cfinke/Construction-grade-Backhoe-Loader/assets/Chassis Back.stl

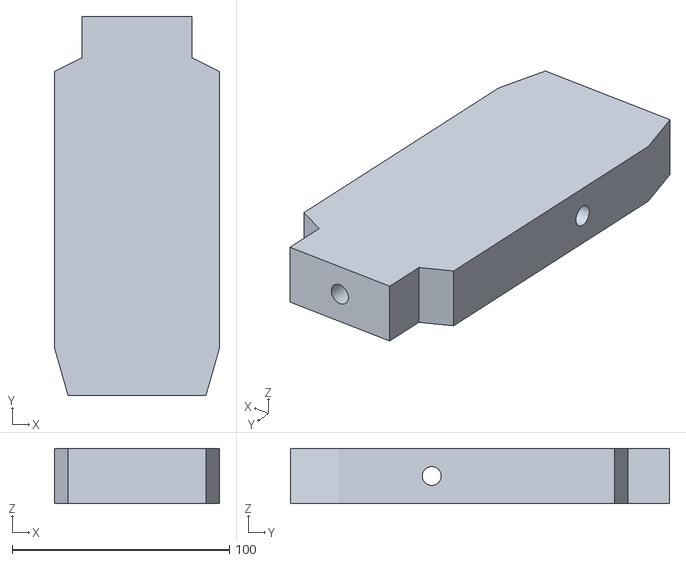
[picture p16: CAD file, 2014-10-20]
assets/Chassis Back.stl
76.2 x 174.6 x 25.4
