cfinke/Construction-grade-Backhoe-Loader/assets/Bucket.stl

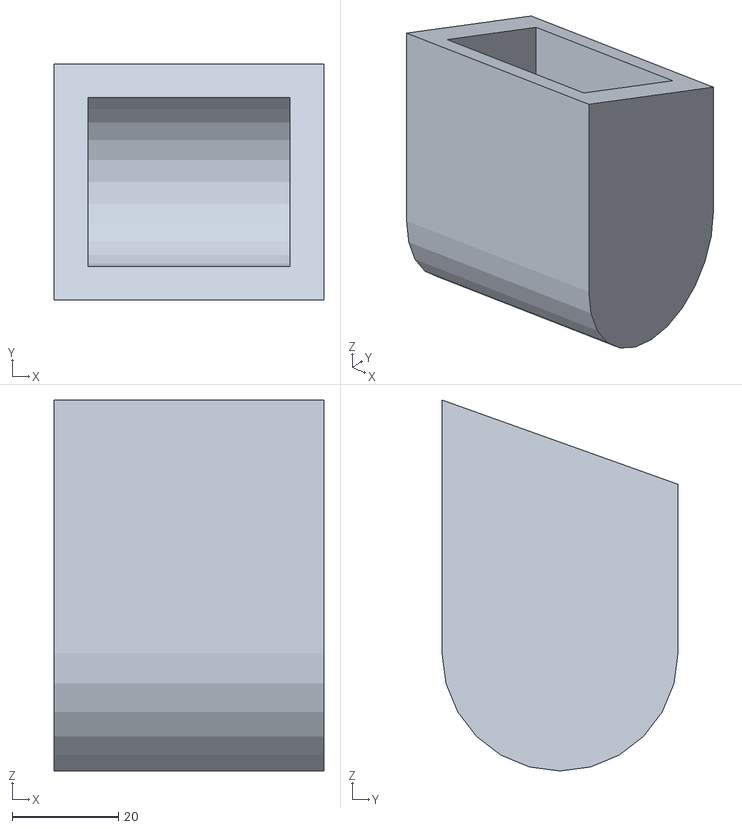
[picture p17: CAD file, 2014-10-20]
assets/Bucket.stl
50.8 x 44.4 x 69.9
