cfinke/Construction-grade-Backhoe-Loader/assets/Loader.stl

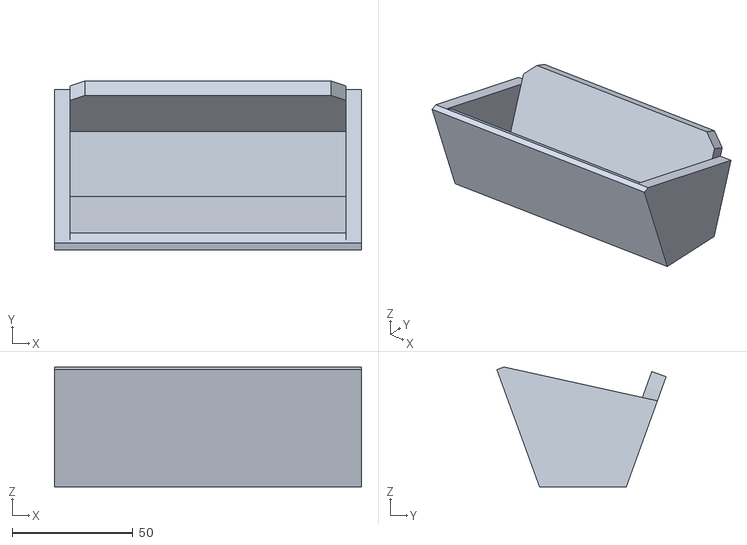
[picture p18: CAD file, 2014-10-20]
assets/Loader.stl
127.0 x 70.1 x 49.6
