cfinke/Construction-grade-Backhoe-Loader/assets/Loader Arm.stl

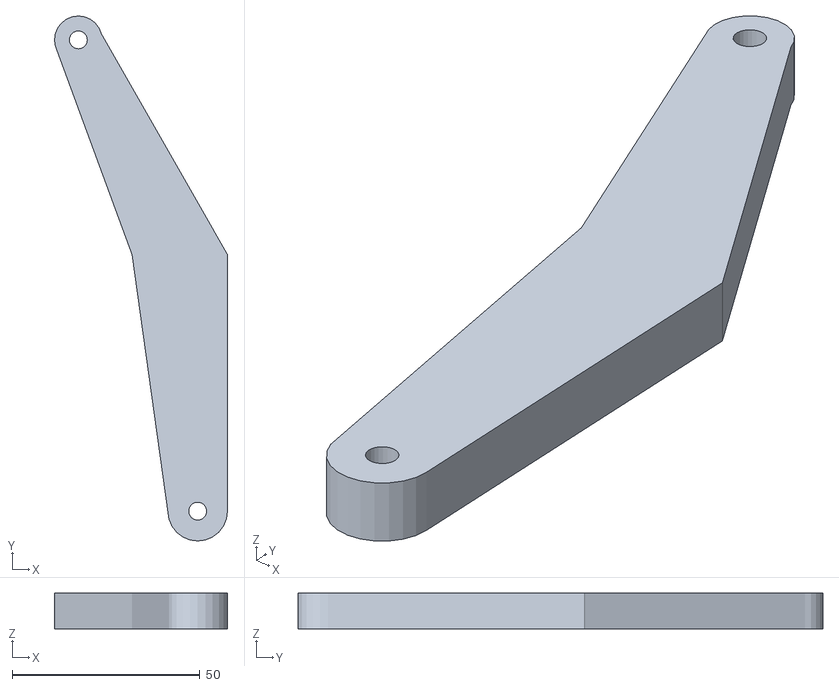
[picture p19: CAD file, 2014-10-20]
assets/Loader Arm.stl
46.0 x 139.7 x 9.52
