cfinke/Construction-grade-Backhoe-Loader/assets/Stick.stl

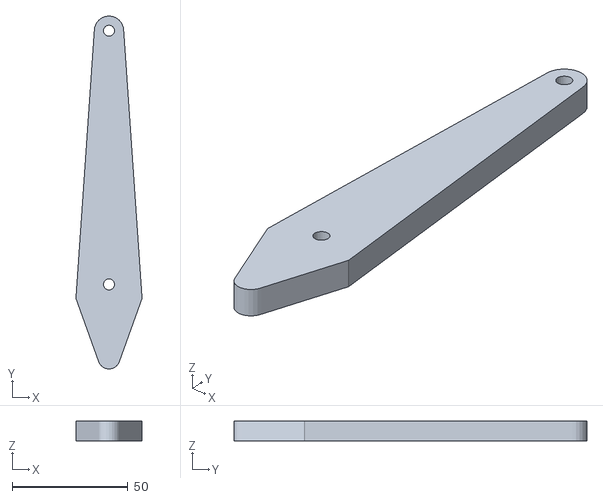
[picture p20: CAD file, 2014-10-20]
assets/Stick.stl
28.6 x 152.4 x 8.47
