cfinke/Construction-grade-Backhoe-Loader/assets/Front Axle.stl

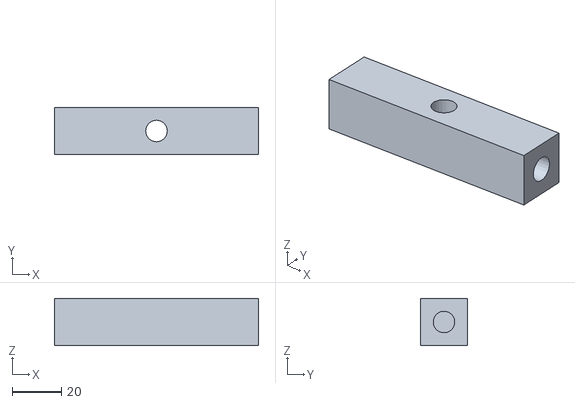
[picture p21: CAD file, 2014-10-20]
assets/Front Axle.stl
82.5 x 19.0 x 19.0
