cfinke/Construction-grade-Backhoe-Loader/assets/Hood.stl

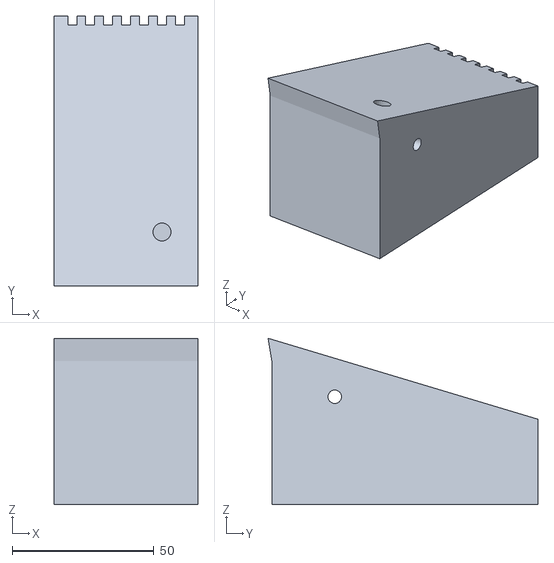
[picture p22: CAD file, 2014-10-20]
assets/Hood.stl
50.8 x 95.2 x 58.7
