cfinke/Construction-grade-Backhoe-Loader/assets/Step.stl

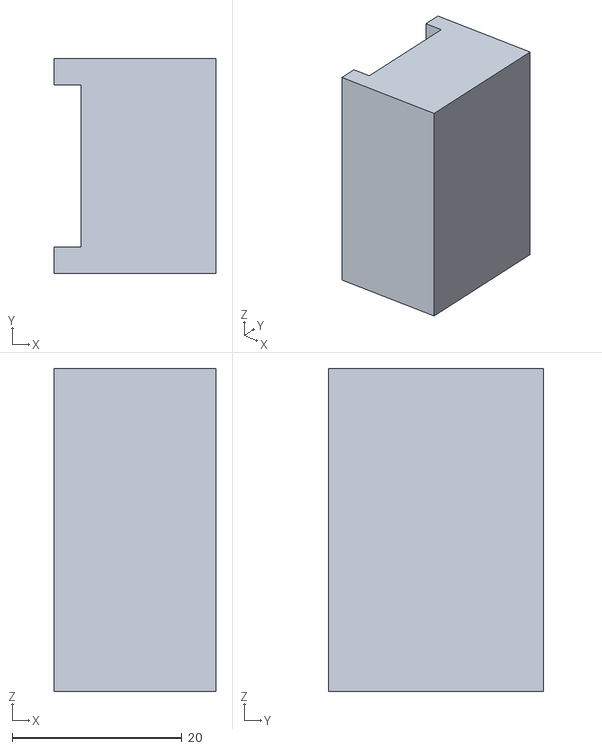
[picture p23: CAD file, 2014-10-20]
assets/Step.stl
19.0 x 25.4 x 38.1
