cfinke/Construction-grade-Backhoe-Loader/assets/Chassis Back Hollow Bottom.stl

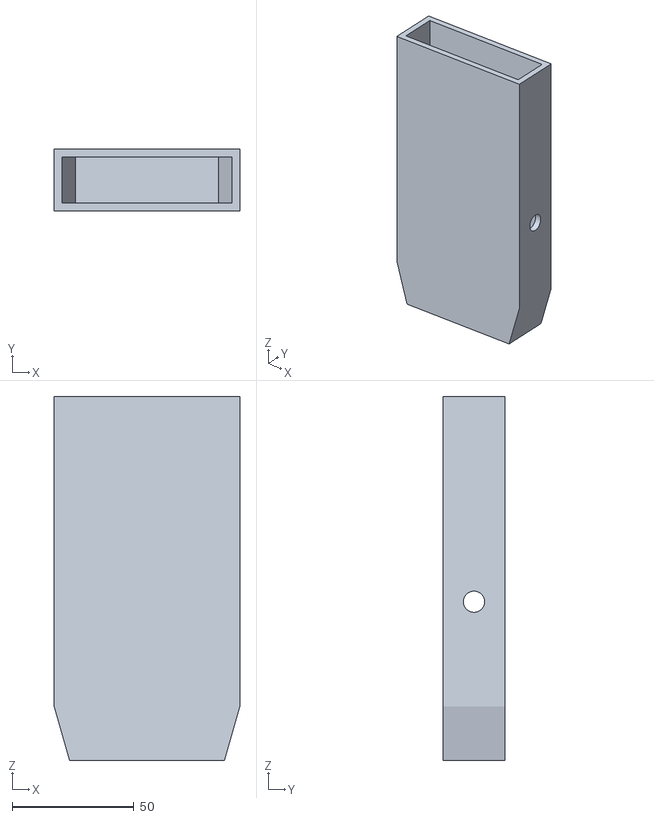
[picture p24: CAD file, 2014-10-20]
assets/Chassis Back Hollow Bottom.stl
76.2 x 25.4 x 149.2
