cfinke/Construction-grade-Backhoe-Loader/assets/Roof.stl

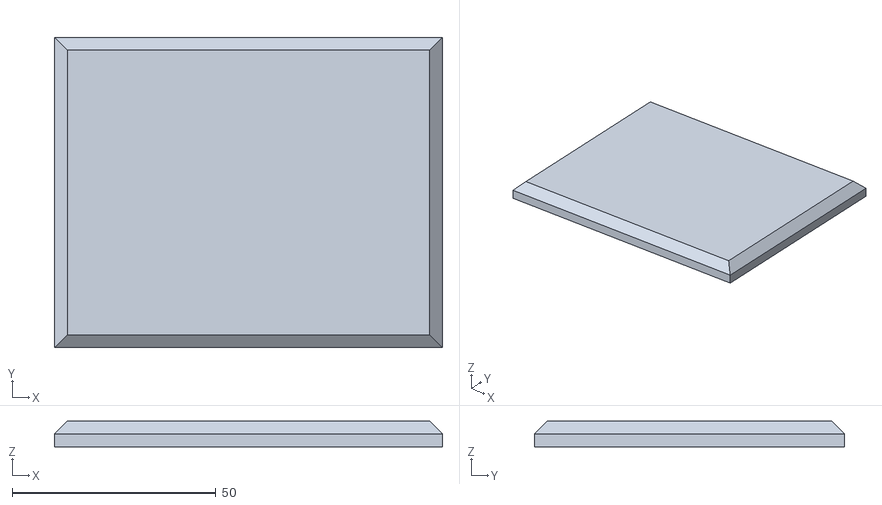
[picture p25: CAD file, 2014-10-20]
assets/Roof.stl
95.2 x 76.2 x 6.35
