cfinke/Construction-grade-Backhoe-Loader/assets/Cab Top.stl

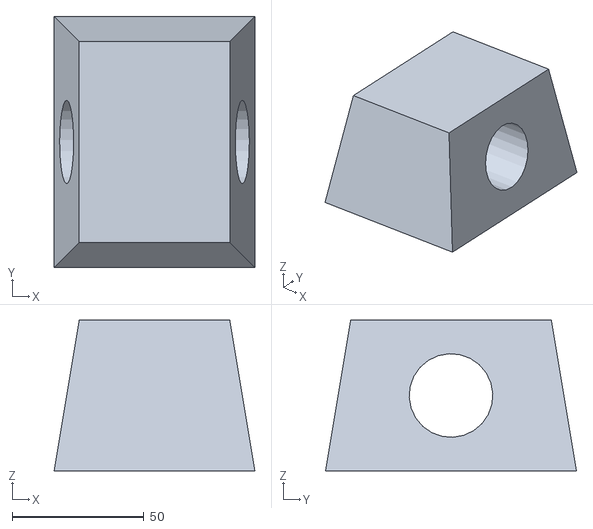
[picture p26: CAD file, 2014-10-20]
assets/Cab Top.stl
76.2 x 95.2 x 57.1
